kvriet/Tablet-pedal/Pictures/turner-corner-view-clear-pedals-springs-visible.png

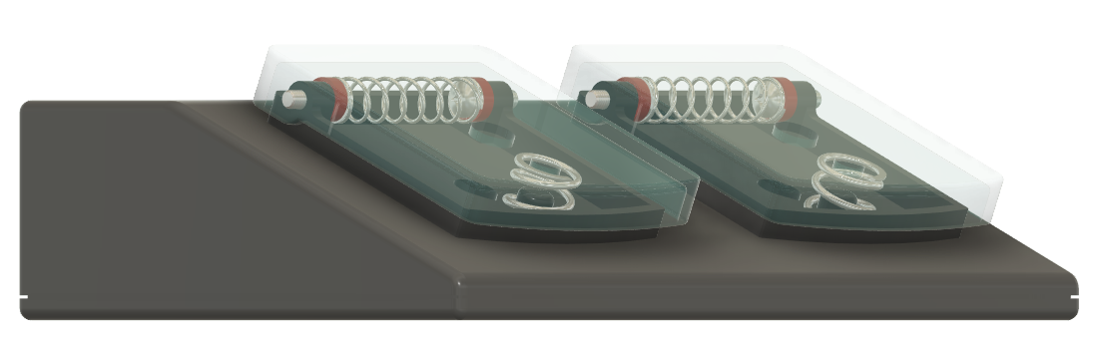
Pictures/turner-corner-view-clear-pedals-springs-visible.png
