kvriet/Tablet-pedal/Circuit KiCAD/Pedal turner circuit/Pedal turner circuit.kicad_sch

## KiCad design Circuit KiCAD/Pedal turner circuit/Pedal turner circuit.kicad_sch (2023-10-11)

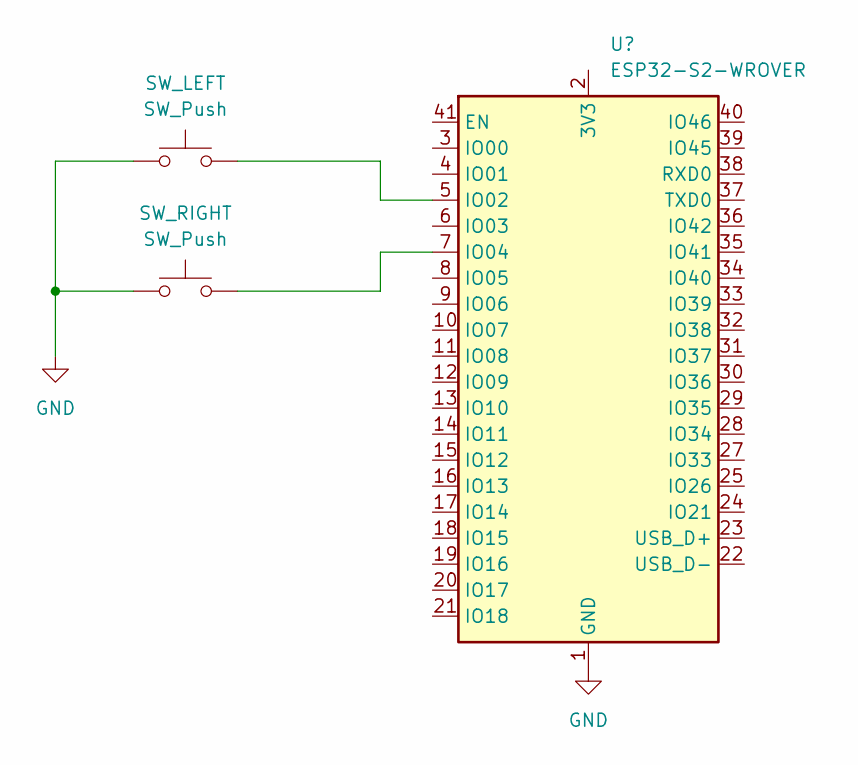
[picture p14: schematic Pedal turner circuit.kicad_sch]

Parts:
SW_LEFT: SW_Push
SW_RIGHT: SW_Push

Connections:
unnamed: SW_LEFT.1, SW_RIGHT.1
