kvriet/Tablet-pedal/Assembly/internal assembly.png

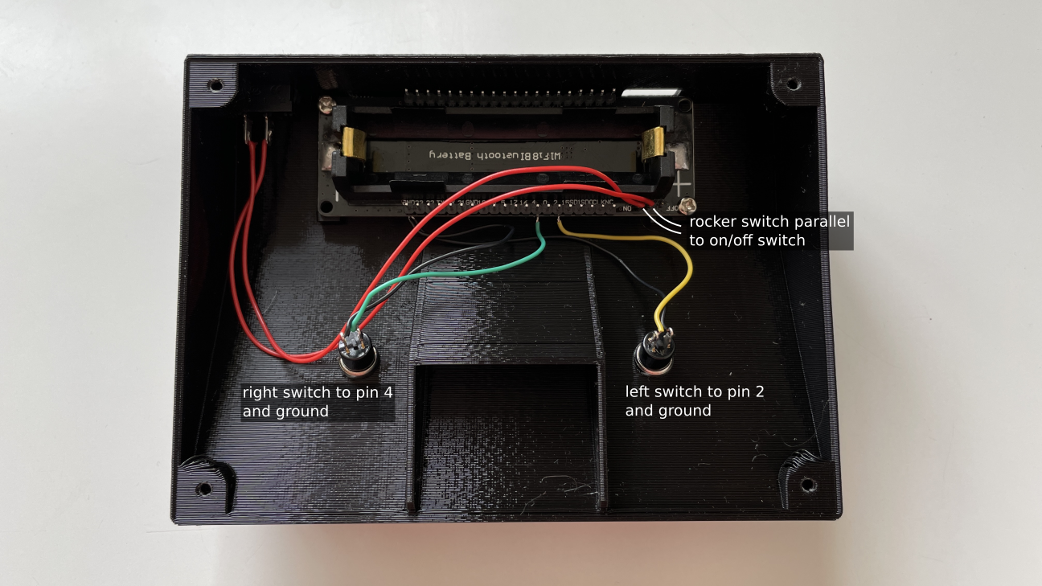
Assembly/internal assembly.png
